SharkbombAudio/Womble/wombleReference/IMG-5375.jpg

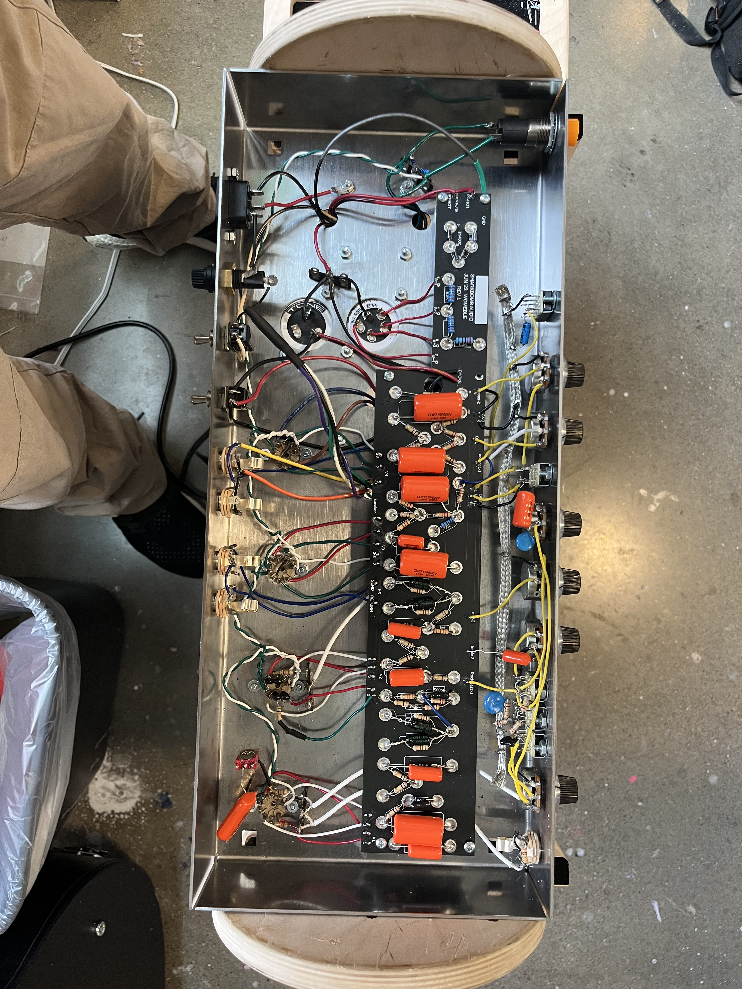
wombleReference/IMG-5375.jpg
