SharkbombAudio/Womble/wombleReference/IMG-5377.jpg

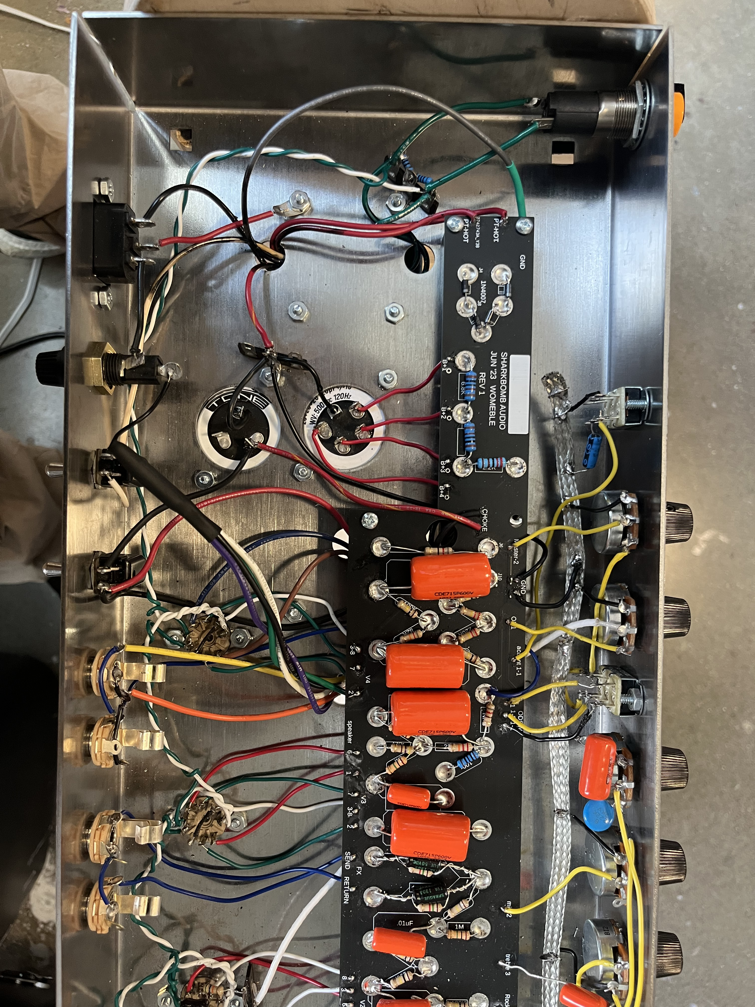
wombleReference/IMG-5377.jpg
